ardavan-p/elec-491/gui/assets/gui_visual_v1.png

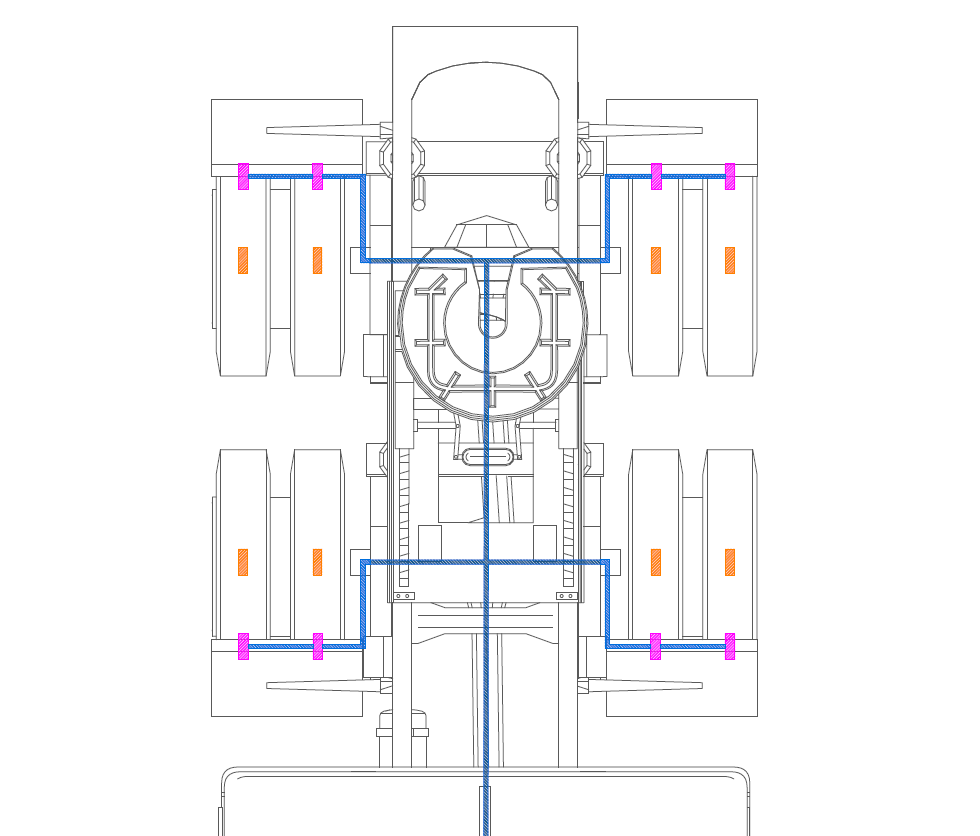
gui/assets/gui_visual_v1.png
