ardavan-p/elec-491/heat_map/tire.png

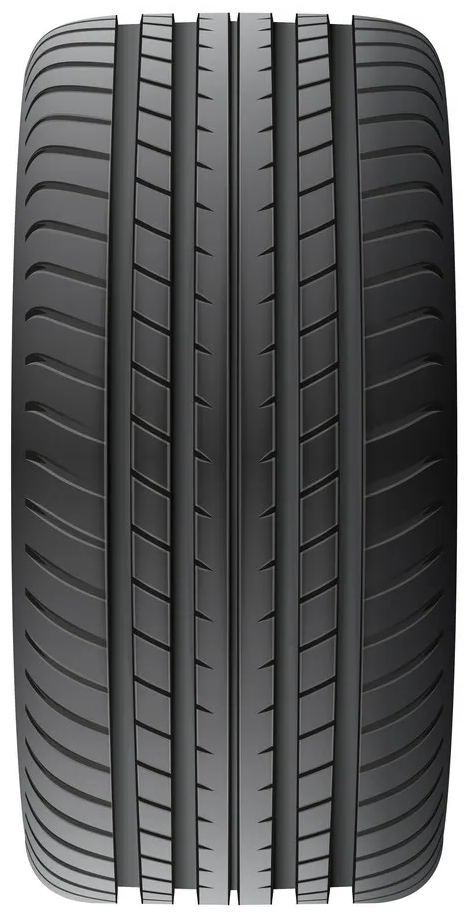
heat_map/tire.png
