ardavan-p/elec-491/heat_map/tire_cropped.png

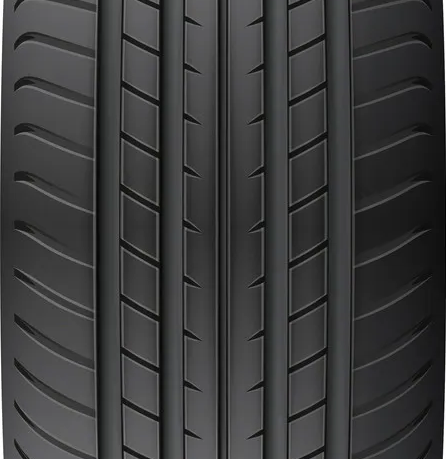
heat_map/tire_cropped.png
