ardavan-p/elec-491/heat_map/tire_rotated.png

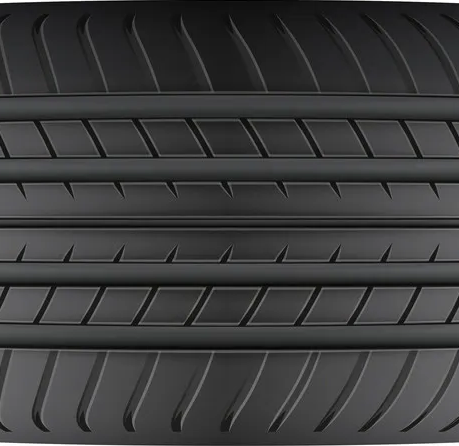
heat_map/tire_rotated.png
