ardavan-p/elec-491/heat_map/top-view-realistic-rubber-tire-symbol-vector-29433454.png

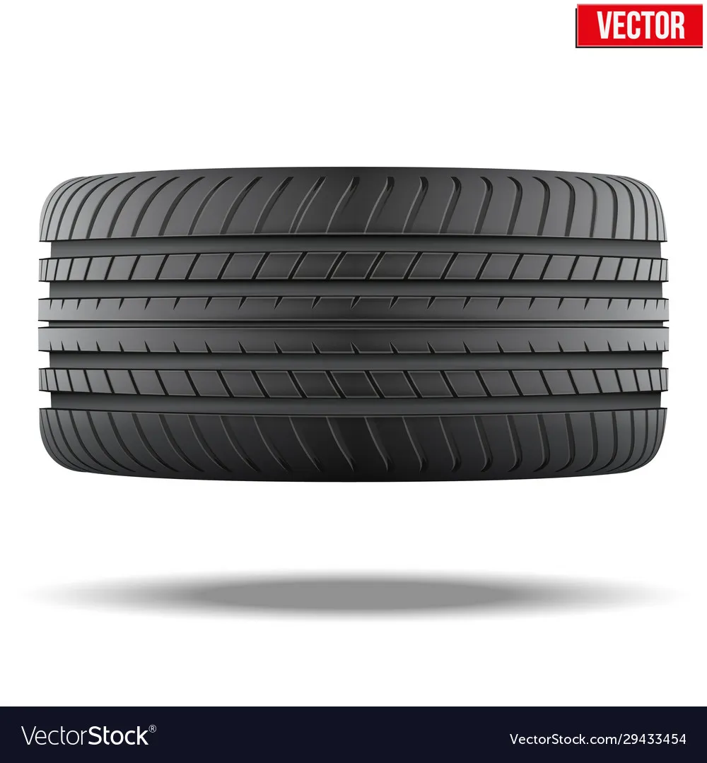
heat_map/top-view-realistic-rubber-tire-symbol-vector-29433454.png
