ardavan-p/elec-491/video/3d_animation/truck clip.PNG

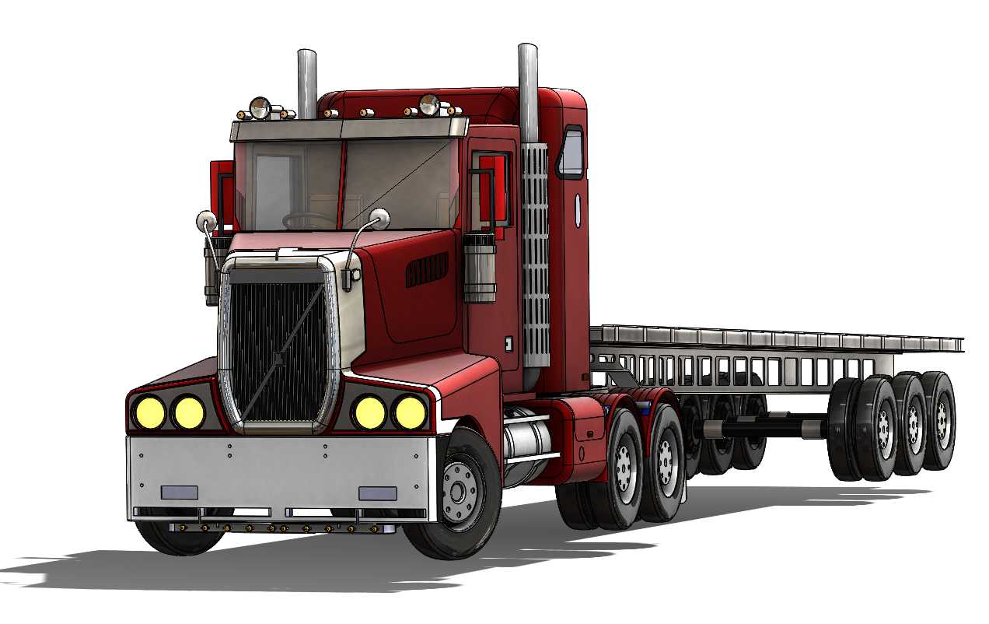
video/3d_animation/truck clip.PNG
