ardavan-p/elec-491/video/3d_animation/truck side view.PNG

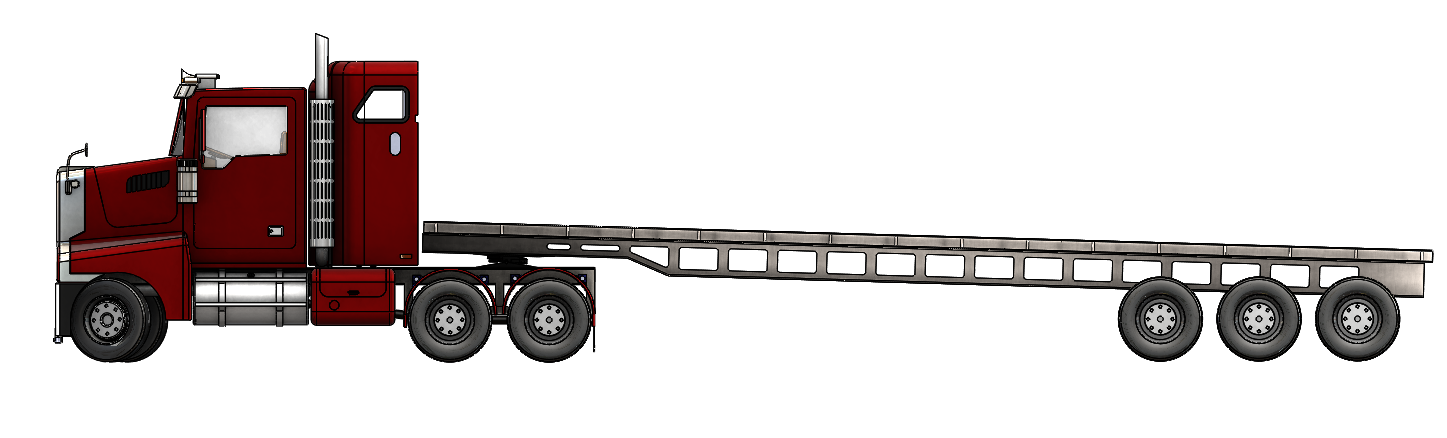
video/3d_animation/truck side view.PNG
