ardavan-p/elec-491/video/scene1/title_screen.png

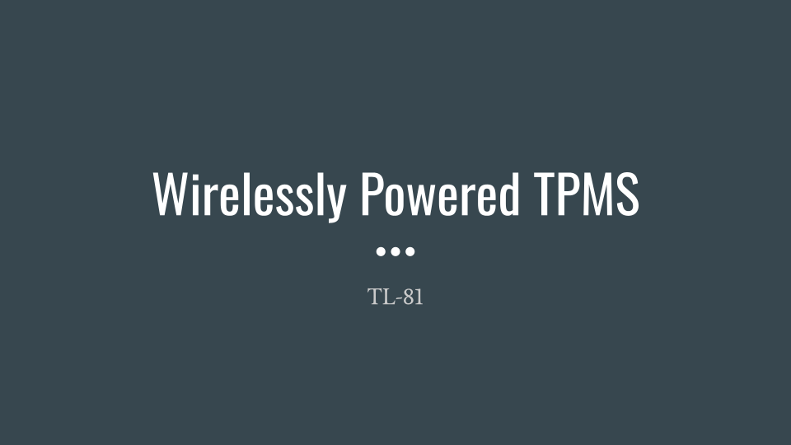
video/scene1/title_screen.png
