ardavan-p/elec-491/video/scene3/ptn_image_v2.png

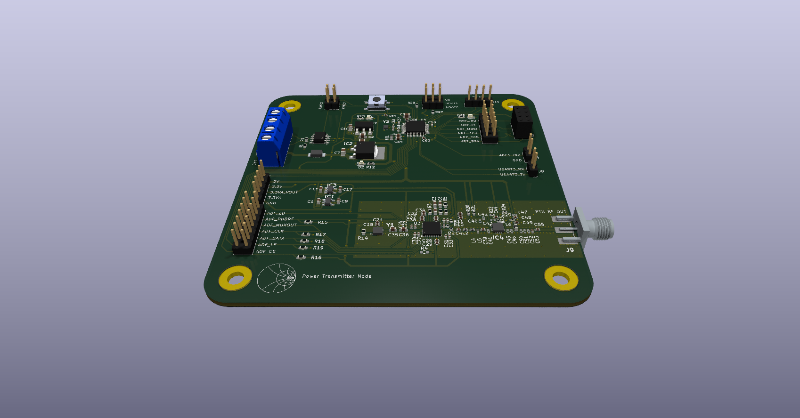
video/scene3/ptn_image_v2.png
