ardavan-p/elec-491/video/scene5/ECE.png

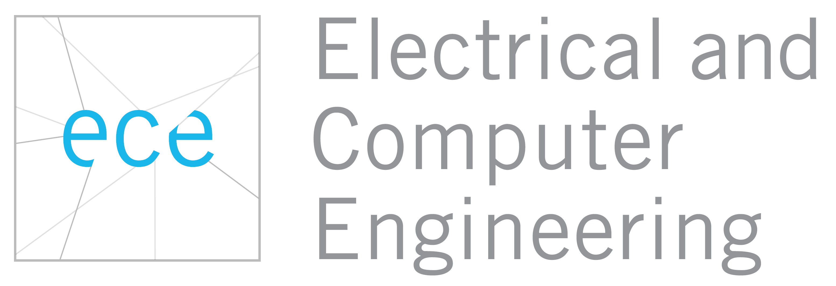
video/scene5/ECE.png
