ardavan-p/elec-491/enclosure/ptn/nRF_PCB.SLDPRT

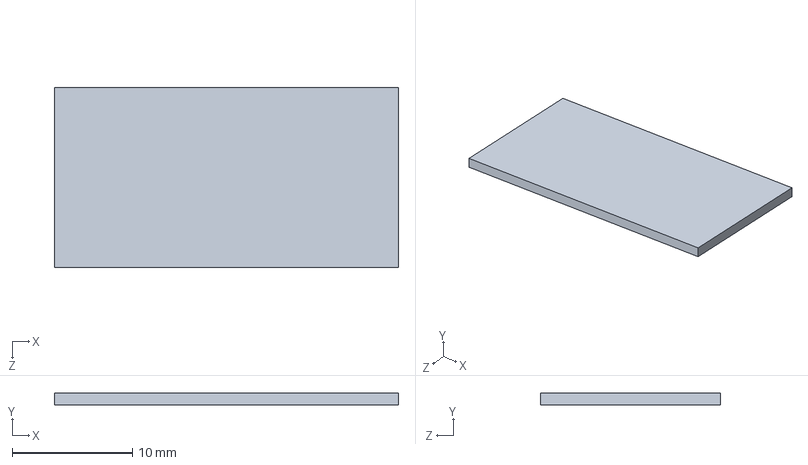
[picture p16: CAD file, 2024-08-16]
enclosure/ptn/nRF_PCB.SLDPRT
28.6 x 1.00 x 15.0 mm
