ardavan-p/elec-491/sn/footprints/capacitors/LIB_T520Y477M006ATE035/T520Y477M006ATE035/3D/T520Y477M006ATE035.stp

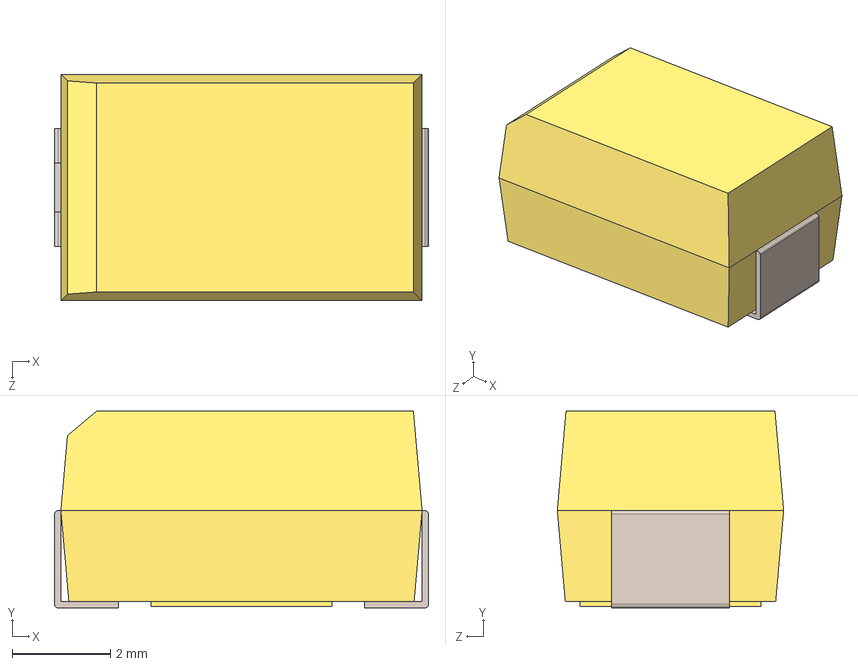
[picture p17: CAD file, 2024-07-30]
sn/footprints/capacitors/LIB_T520Y477M006ATE035/T520Y477M006ATE035/3D/T520Y477M006ATE035.stp
7.60 x 4.00 x 4.60 mm
Case_Bottom_31
Case_Top_31
Case_Cathode_31
Case_Anode_31
