ardavan-p/elec-491/sn/footprints/capacitors/LIB_TPMV108M006R0020/TPMV108M006R0020/3D/TPMV108M006R0020.stp

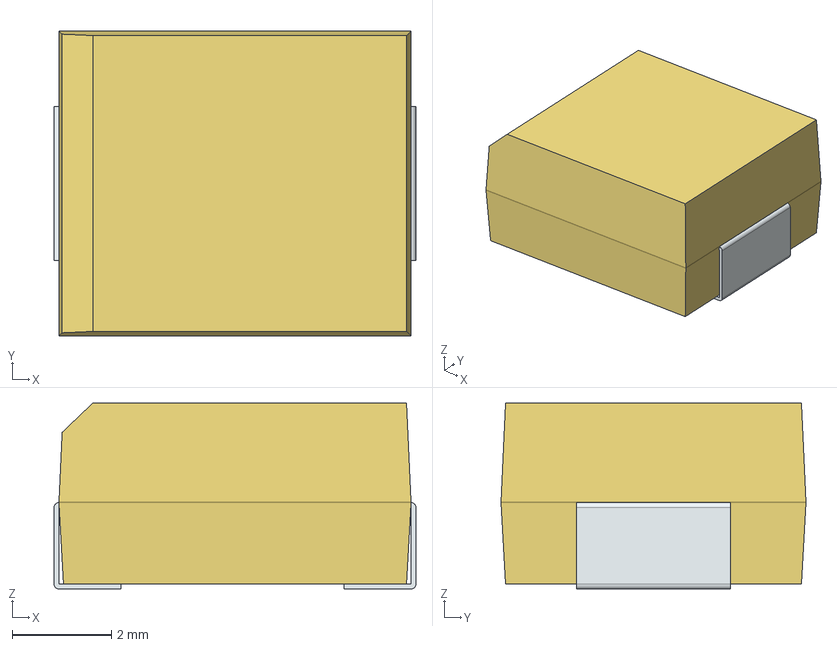
[picture p18: CAD file, 2024-07-30]
sn/footprints/capacitors/LIB_TPMV108M006R0020/TPMV108M006R0020/3D/TPMV108M006R0020.stp
7.30 x 6.15 x 3.75 mm
FilletPin1
FilletPin2
