ardavan-p/elec-491/sn/footprints/capacitors/LIB_TR3W108M6R3C0050/TR3W108M6R3C0050/3D/TR3W108M6R3C0050.stp

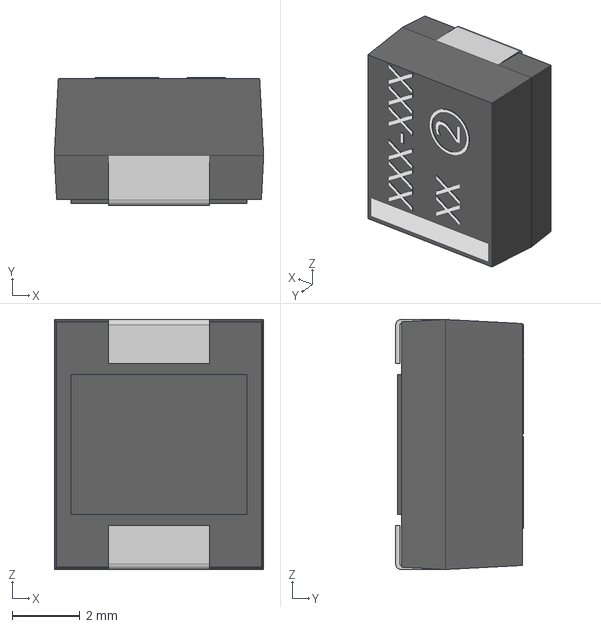
[picture p19: CAD file, 2024-07-30]
sn/footprints/capacitors/LIB_TR3W108M6R3C0050/TR3W108M6R3C0050/3D/TR3W108M6R3C0050.stp
6.20 x 3.78 x 7.40 mm
