ardavan-p/elec-491/sn/footprints/CONSMA020_062_G/CONSMA020.062-G.step

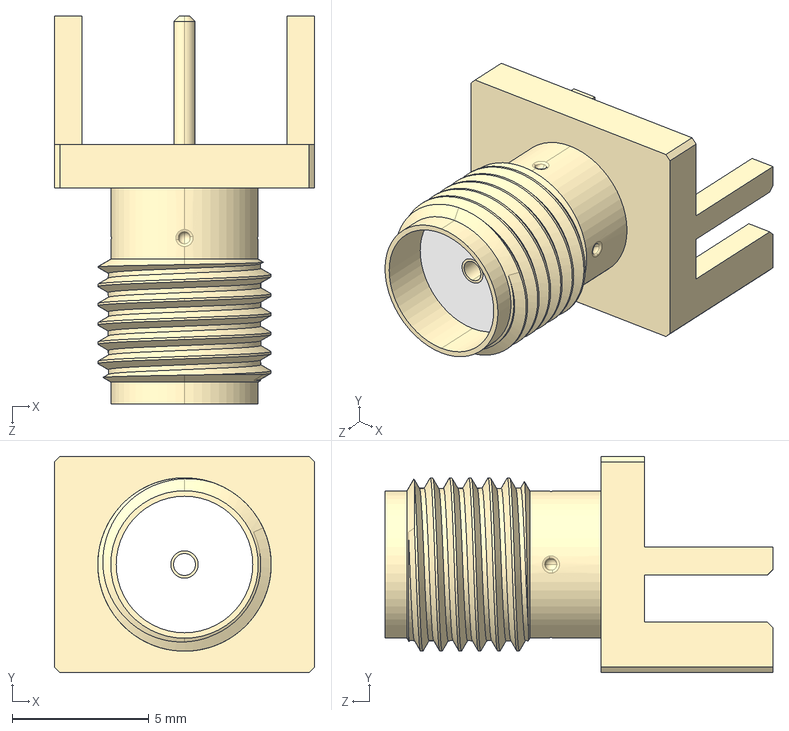
[picture p20: CAD file, 2024-07-30]
sn/footprints/CONSMA020_062_G/CONSMA020.062-G.step
9.52 x 7.92 x 14.2 mm
