ardavan-p/elec-491/sn/footprints/LIB_381LX473M016A452/381LX473M016A452/3D/381LX473M016A452.stp

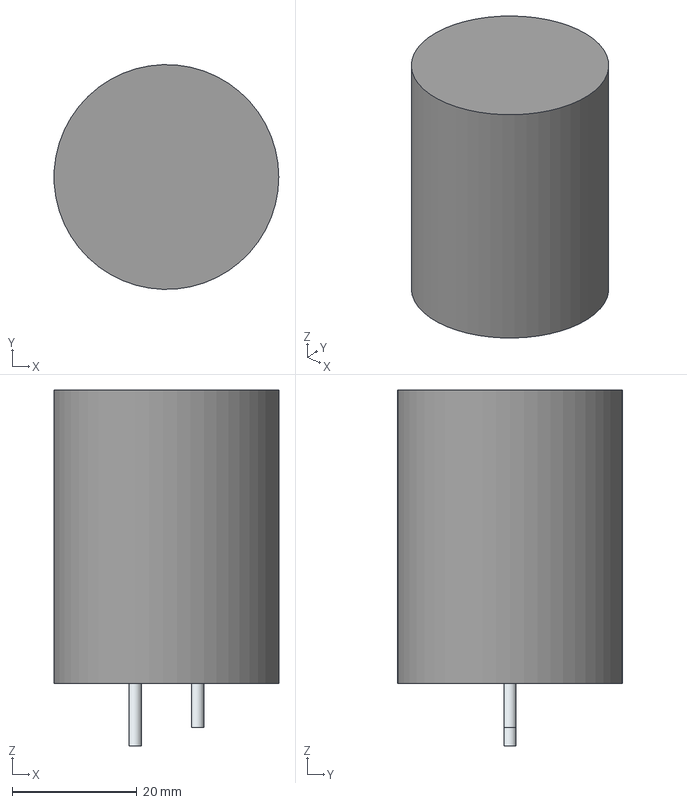
[picture p21: CAD file, 2024-07-30]
sn/footprints/LIB_381LX473M016A452/381LX473M016A452/3D/381LX473M016A452.stp
36.0 x 36.0 x 57.0 mm
SimpleBody
Pin1
Pin2
