ardavan-p/elec-491/sn/footprints/LIB_500SSP1S1M6QEB/500SSP1S1M6QEB/3D/500SSP1S1M6QEB.stp

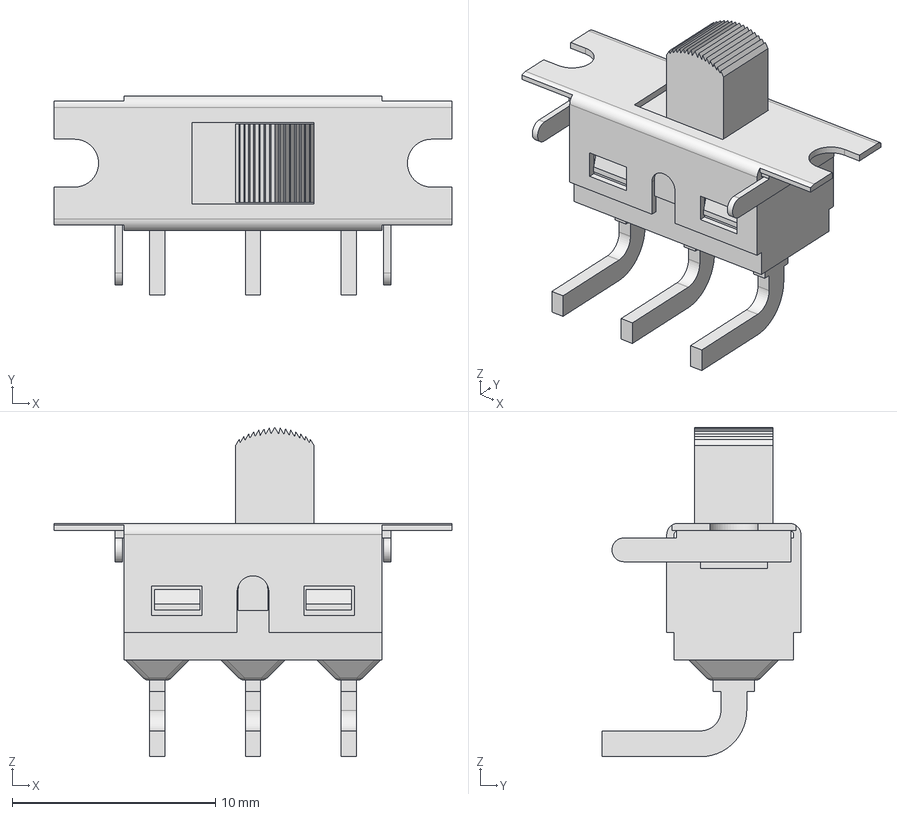
[picture p22: CAD file, 2024-07-30]
sn/footprints/LIB_500SSP1S1M6QEB/500SSP1S1M6QEB/3D/500SSP1S1M6QEB.stp
19.6 x 9.78 x 16.2 mm
