ardavan-p/elec-491/sn/footprints/LIB_901-10309/901-10309/3D/901-10309.stp

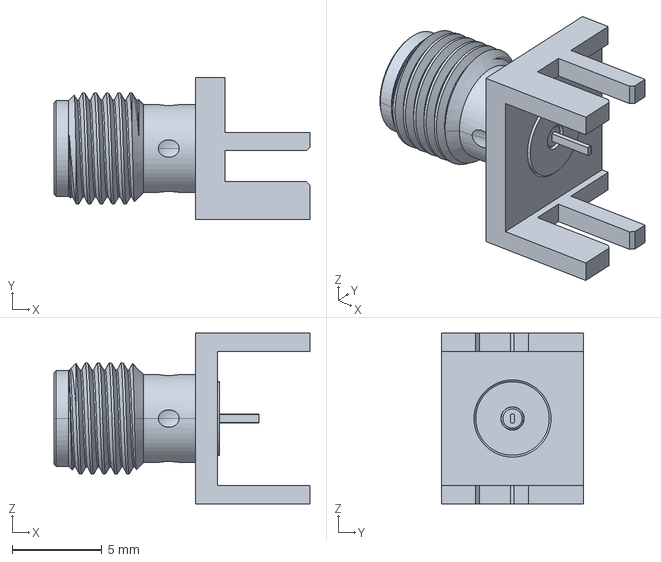
[picture p23: CAD file, 2024-07-30]
sn/footprints/LIB_901-10309/901-10309/3D/901-10309.stp
14.3 x 7.92 x 9.52 mm
