ardavan-p/elec-491/sn/footprints/LIB_AD8226ARMZ/AD8226ARMZ/3D/AD8226ARMZ.stp

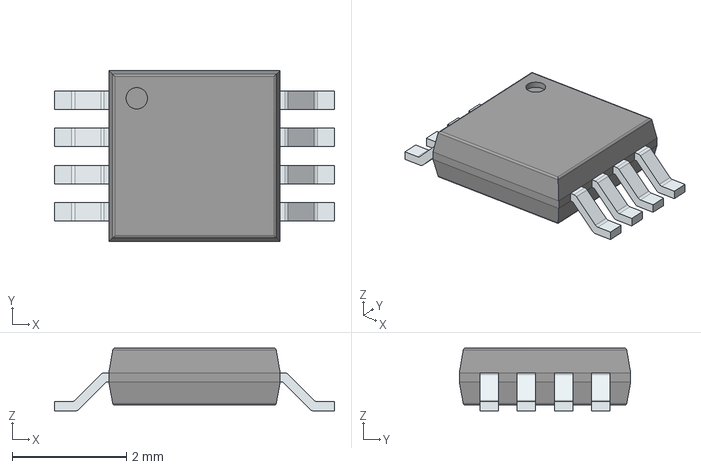
[picture p24: CAD file, 2024-07-30]
sn/footprints/LIB_AD8226ARMZ/AD8226ARMZ/3D/AD8226ARMZ.stp
4.90 x 3.00 x 1.10 mm
PinsArrayLR
