ardavan-p/elec-491/sn/footprints/LIB_AYZ0102AGRLC/AYZ0102AGRLC/3D/AYZ0102AGRLC.stp

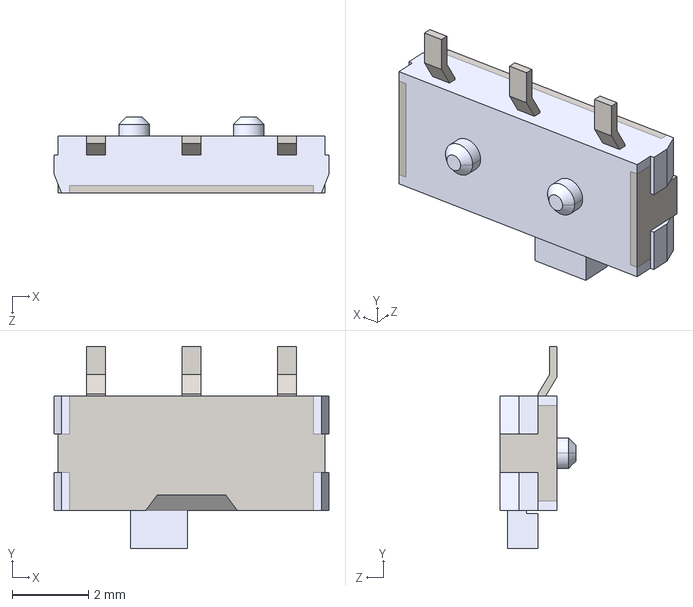
[picture p25: CAD file, 2024-07-30]
sn/footprints/LIB_AYZ0102AGRLC/AYZ0102AGRLC/3D/AYZ0102AGRLC.stp
7.20 x 5.30 x 2.00 mm
