ardavan-p/elec-491/sn/footprints/LIB_B3FS-1002P/B3FS-1002P/3D/B3FS-1002P.stp

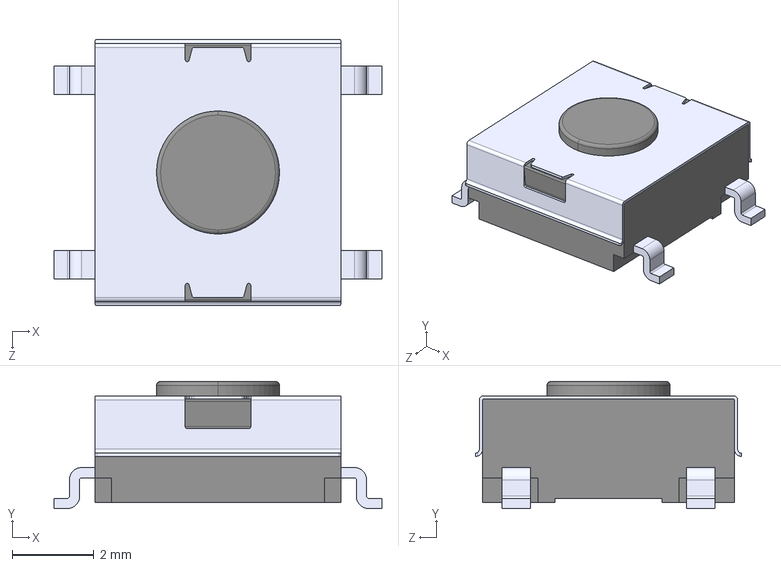
[picture p26: CAD file, 2024-07-30]
sn/footprints/LIB_B3FS-1002P/B3FS-1002P/3D/B3FS-1002P.stp
8.00 x 3.10 x 6.50 mm
