ardavan-p/elec-491/sn/footprints/LIB_CAS-120A1/CAS-120A1/3D/CAS-120A1.stp

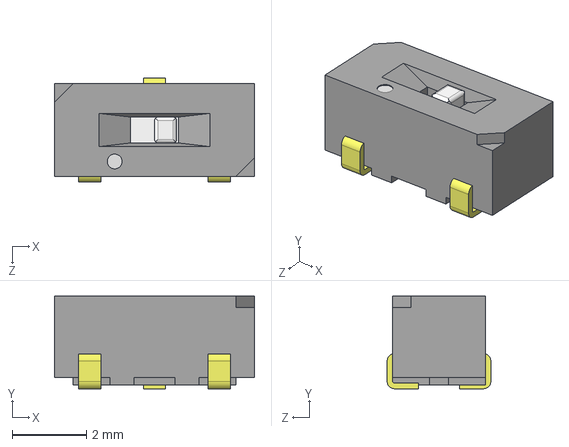
[picture p27: CAD file, 2024-07-30]
sn/footprints/LIB_CAS-120A1/CAS-120A1/3D/CAS-120A1.stp
5.40 x 2.50 x 2.80 mm
1 pole_s
CAS_c_12A
