ardavan-p/elec-491/sn/footprints/LIB_EEE-FP0J102AL/EEE-FP0J102AL/3D/EEE-FP0J102AL.stp

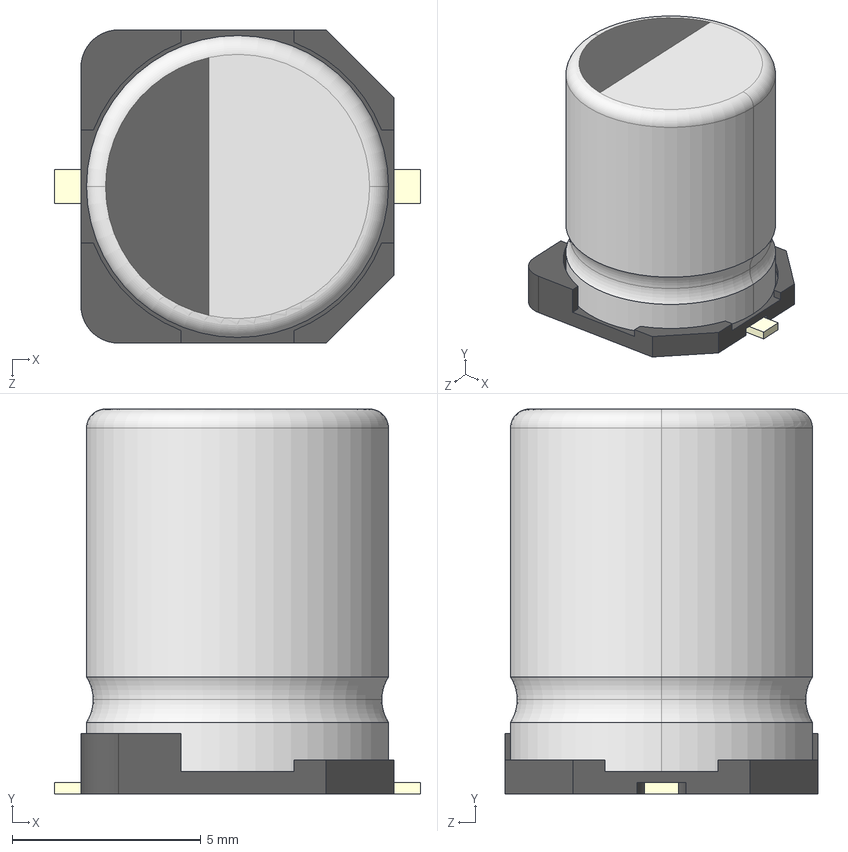
[picture p28: CAD file, 2024-07-30]
sn/footprints/LIB_EEE-FP0J102AL/EEE-FP0J102AL/3D/EEE-FP0J102AL.stp
9.70 x 10.2 x 8.30 mm
標準SIZE CODE F-001
標準SIZE CODE F-002
標準SIZE CODE F-003 x 2
