ardavan-p/elec-491/sn/footprints/LIB_EMPCB.SMAFSTJ.B.HT/EMPCB.SMAFSTJ.B.HT/3D/EMPCB.SMAFSTJ.B.HT.stp

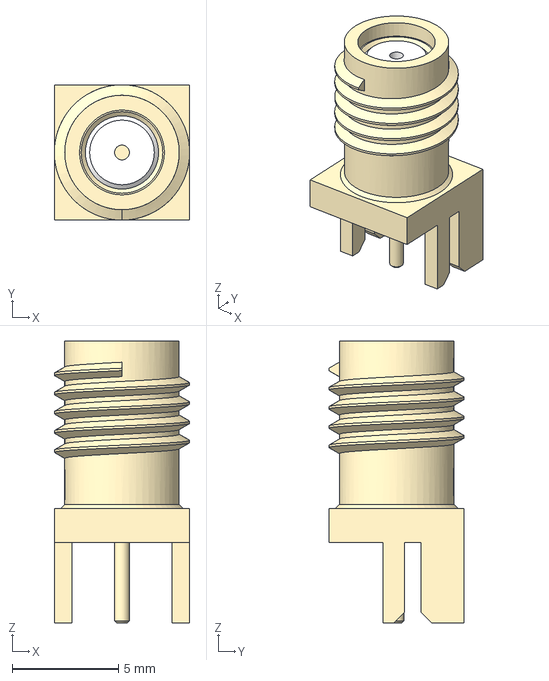
[picture p29: CAD file, 2024-07-30]
sn/footprints/LIB_EMPCB.SMAFSTJ.B.HT/EMPCB.SMAFSTJ.B.HT/3D/EMPCB.SMAFSTJ.B.HT.stp
6.38 x 6.39 x 13.3 mm
