ardavan-p/elec-491/sn/footprints/LIB_FME0H473ZF/FME0H473ZF/3D/FME0H473ZF.stp

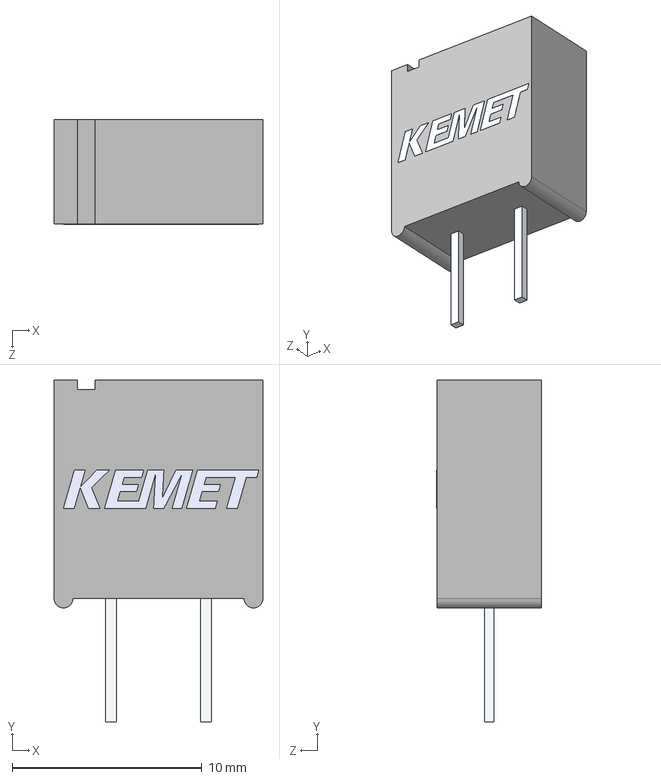
[picture p30: CAD file, 2024-07-30]
sn/footprints/LIB_FME0H473ZF/FME0H473ZF/3D/FME0H473ZF.stp
11.0 x 18.0 x 5.50 mm
