ardavan-p/elec-491/sn/footprints/LIB_NPP-301A-700AT/NPP-301A-700AT/3D/NPP-301A-700AT.stp

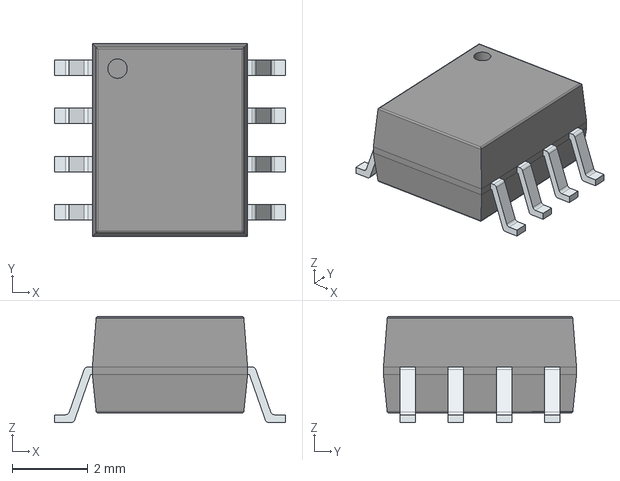
[picture p31: CAD file, 2024-07-30]
sn/footprints/LIB_NPP-301A-700AT/NPP-301A-700AT/3D/NPP-301A-700AT.stp
6.10 x 5.10 x 2.80 mm
PinsArrayLR
