ardavan-p/elec-491/sn/footprints/LIB_nRF24L01P/nRF24L01P/3D/nRF24L01P.stp

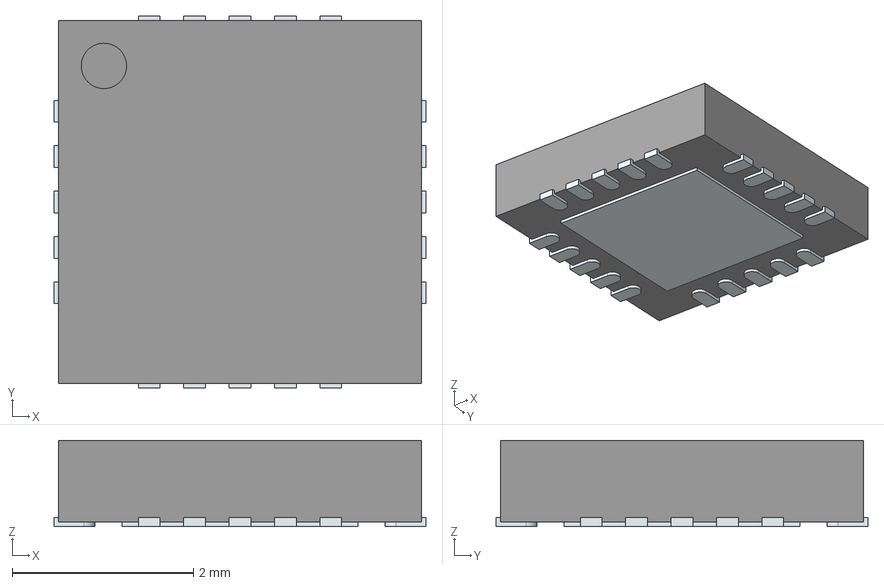
[picture p32: CAD file, 2024-07-30]
sn/footprints/LIB_nRF24L01P/nRF24L01P/3D/nRF24L01P.stp
4.10 x 4.10 x 0.95 mm
ThermalPin
PinsArrayLR
PinsArrayTB
