ardavan-p/elec-491/sn/footprints/LIB_P2110B/P2110B/3D/P2110B.stp

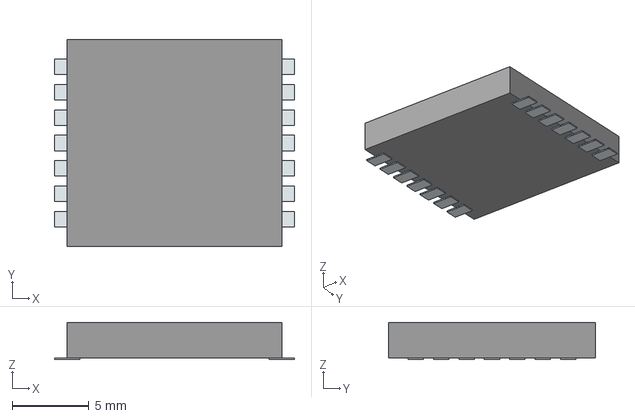
[picture p33: CAD file, 2024-07-30]
sn/footprints/LIB_P2110B/P2110B/3D/P2110B.stp
15.6 x 13.5 x 2.41 mm
Pins
