ardavan-p/elec-491/sn/footprints/LIB_STM32U031K8U6/STM32U031K8U6/3D/STM32U031K8U6.stp

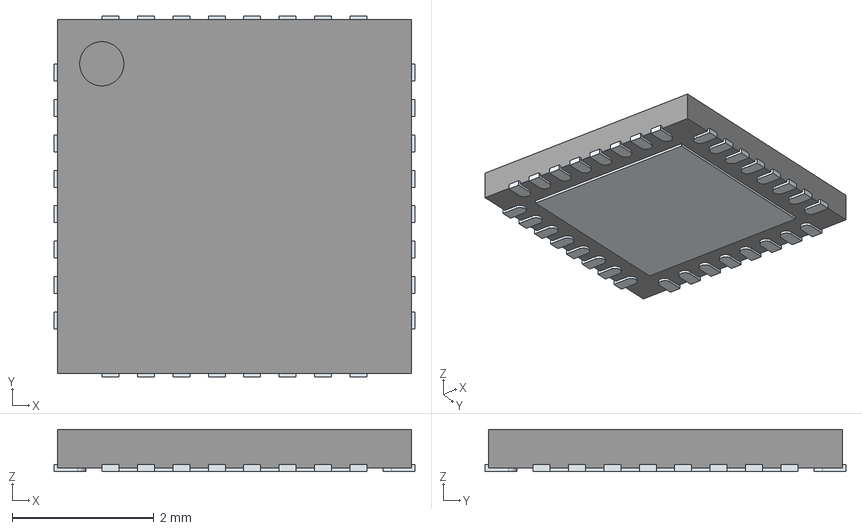
[picture p34: CAD file, 2024-07-30]
sn/footprints/LIB_STM32U031K8U6/STM32U031K8U6/3D/STM32U031K8U6.stp
5.10 x 5.10 x 0.6 mm
ThermalPin
PinsArrayLR
PinsArrayTB
