ardavan-p/elec-491/sn/footprints/LIB_TS21-34-035-BK-160-SMT-TR/TS21-34-035-BK-160-SMT-TR/3D/TS21-34-035-BK-160-SMT-TR.stp

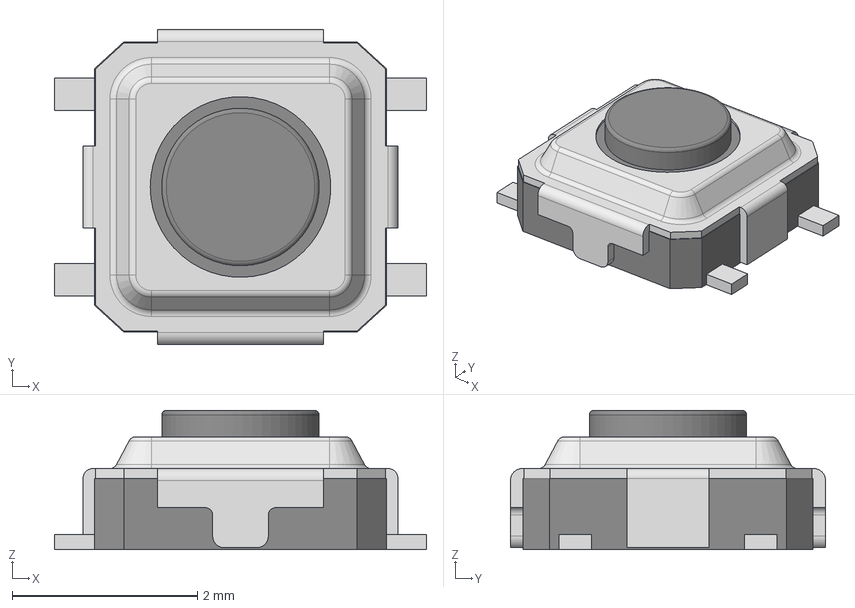
[picture p35: CAD file, 2024-07-30]
sn/footprints/LIB_TS21-34-035-BK-160-SMT-TR/TS21-34-035-BK-160-SMT-TR/3D/TS21-34-035-BK-160-SMT-TR.stp
4.02 x 3.40 x 1.50 mm
