ardavan-p/elec-491/sn/footprints/ul_STM32U031R8T6/LQFP64_STM.step

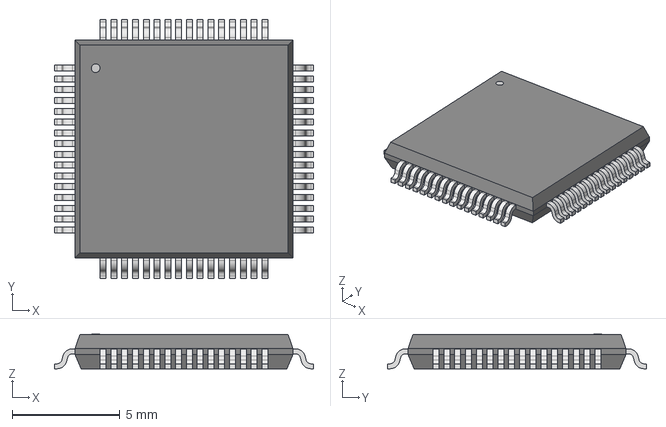
[picture p36: CAD file, 2024-07-30]
sn/footprints/ul_STM32U031R8T6/LQFP64_STM.step
12.0 x 12.0 x 1.60 mm
