ardavan-p/elec-491/video/3d_animation/BGs flatbed 2/mud guard back.SLDPRT

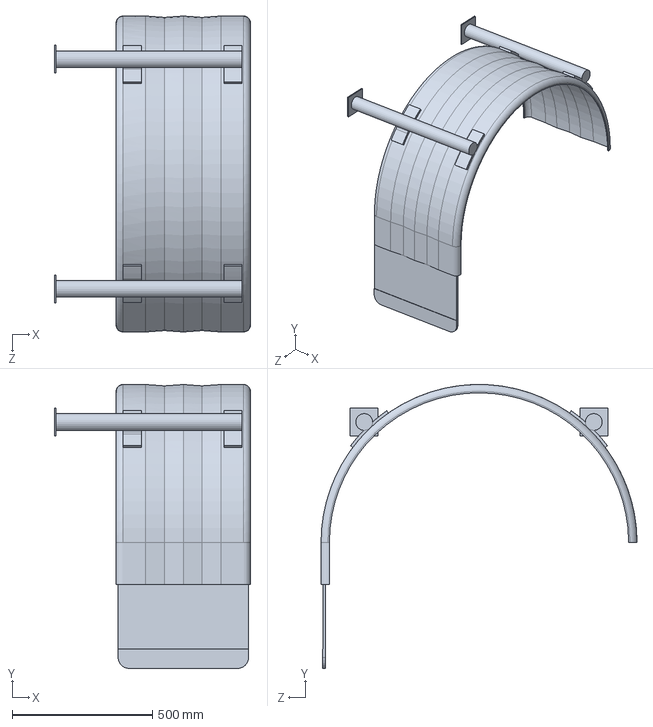
[picture p37: CAD file, 2024-08-16]
video/3d_animation/BGs flatbed 2/mud guard back.SLDPRT
700.0 x 1013.8 x 1128.0 mm
