ardavan-p/elec-491/enclosure/ptn/baseplate.SLDPRT

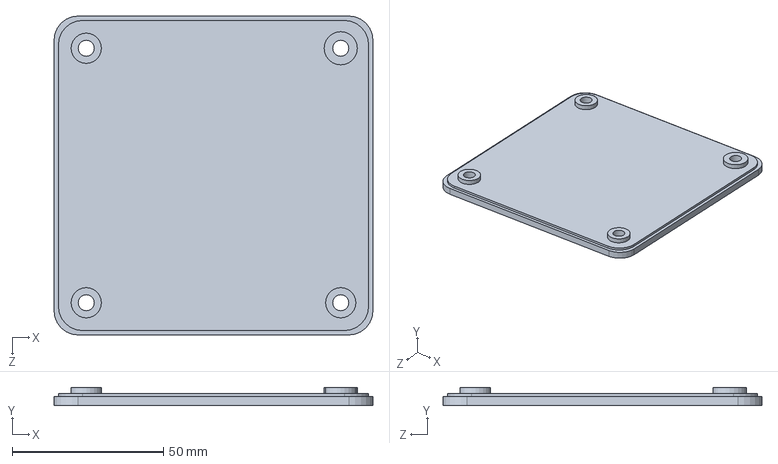
[picture p38: CAD file, 2024-08-16]
enclosure/ptn/baseplate.SLDPRT
105.3 x 6.00 x 105.3 mm
