ardavan-p/elec-491/video/3d_animation/BGs flatbed 2/attachment lock.SLDPRT

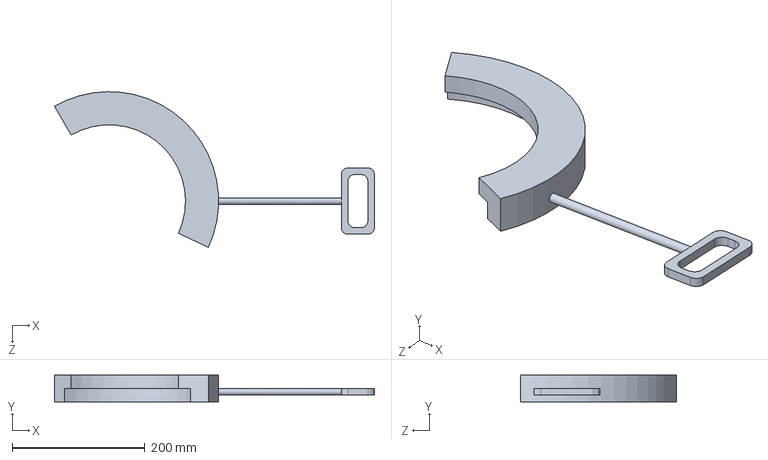
[picture p39: CAD file, 2024-08-16]
video/3d_animation/BGs flatbed 2/attachment lock.SLDPRT
482.5 x 40.0 x 234.7 mm
