ardavan-p/elec-491/enclosure/ptn/top_cover.SLDPRT

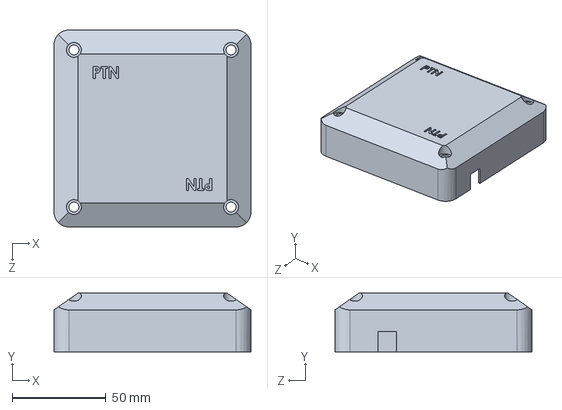
[picture p40: CAD file, 2024-08-16]
enclosure/ptn/top_cover.SLDPRT
105.3 x 31.5 x 105.3 mm
