ardavan-p/elec-491/video/3d_animation/BGs flatbed 2/right door.SLDPRT

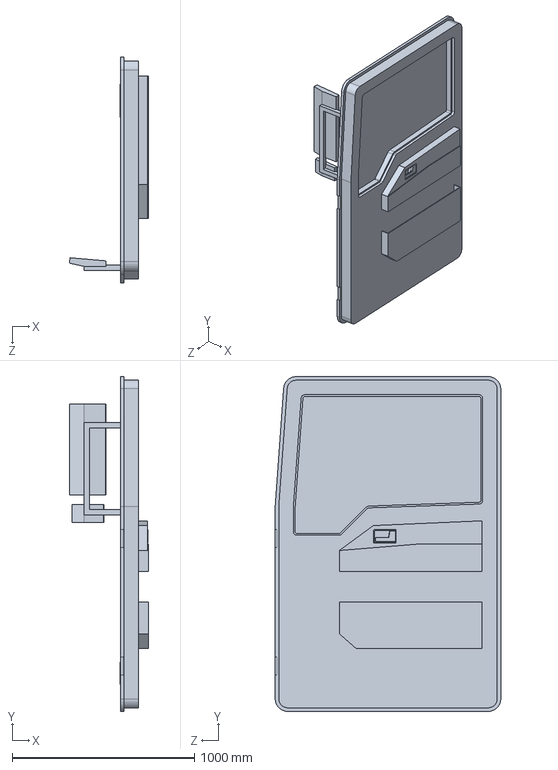
[picture p41: CAD file, 2024-08-16]
video/3d_animation/BGs flatbed 2/right door.SLDPRT
434.2 x 1840.0 x 1240.0 mm
