ardavan-p/elec-491/video/3d_animation/BGs flatbed 2/steering.sldprt

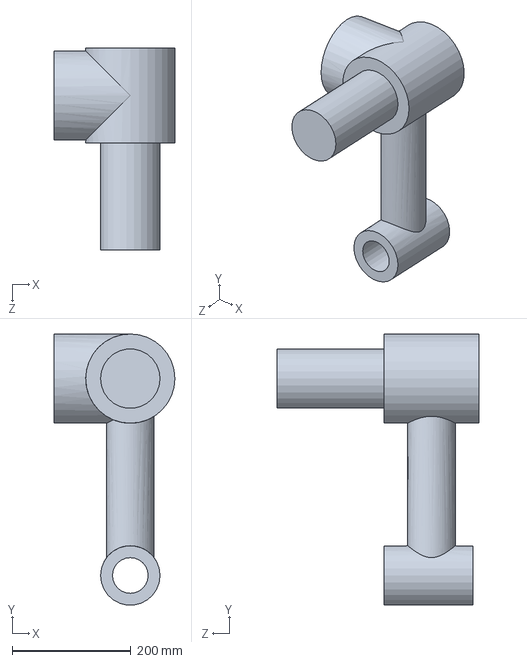
[picture p42: CAD file, 2024-08-16]
video/3d_animation/BGs flatbed 2/steering.sldprt
203.2 x 455.6 x 340.0 mm
