ardavan-p/elec-491/video/3d_animation/BGs flatbed 2/hub.SLDPRT

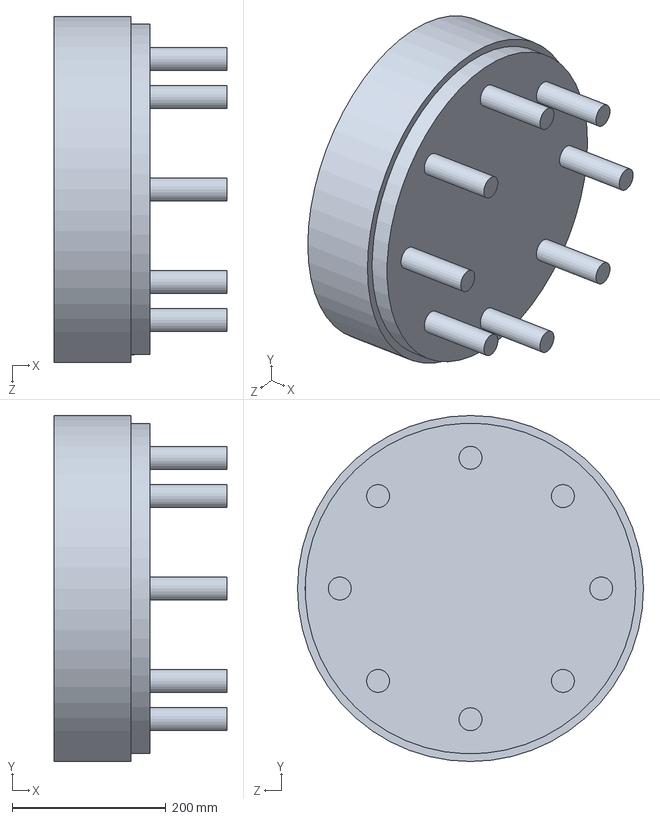
[picture p43: CAD file, 2024-08-16]
video/3d_animation/BGs flatbed 2/hub.SLDPRT
225.0 x 450.0 x 450.0 mm
