ardavan-p/elec-491/video/3d_animation/BGs flatbed 2/tank.SLDPRT

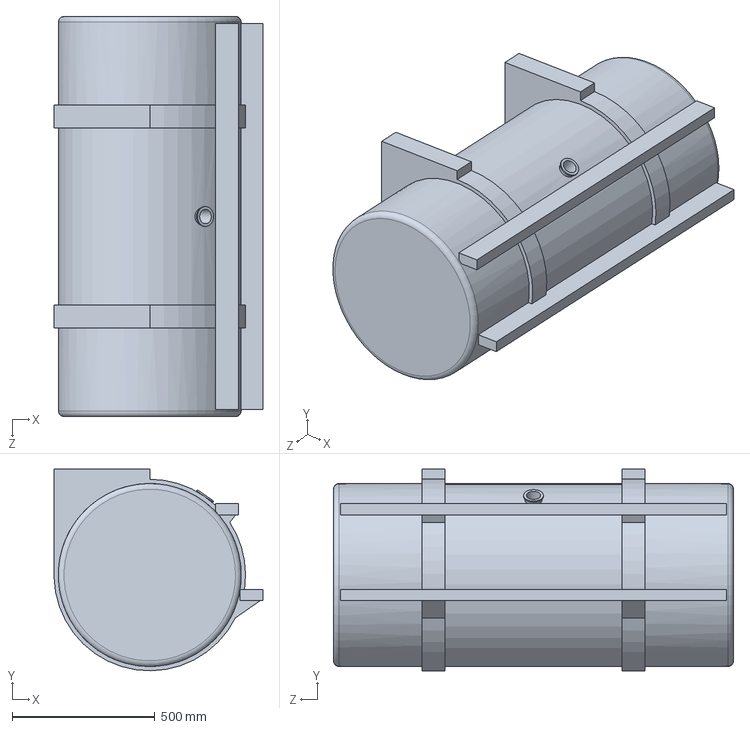
[picture p44: CAD file, 2024-08-16]
video/3d_animation/BGs flatbed 2/tank.SLDPRT
731.1 x 705.0 x 1400.0 mm
