ardavan-p/elec-491/video/3d_animation/BGs flatbed 2/mud guard2 front.SLDPRT

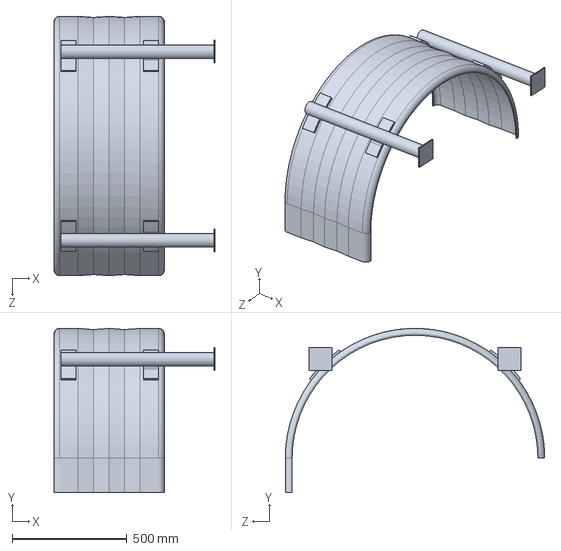
[picture p45: CAD file, 2024-08-16]
video/3d_animation/BGs flatbed 2/mud guard2 front.SLDPRT
700.0 x 713.8 x 1128.0 mm
