ardavan-p/elec-491/video/3d_animation/BGs flatbed 2/cab.SLDPRT

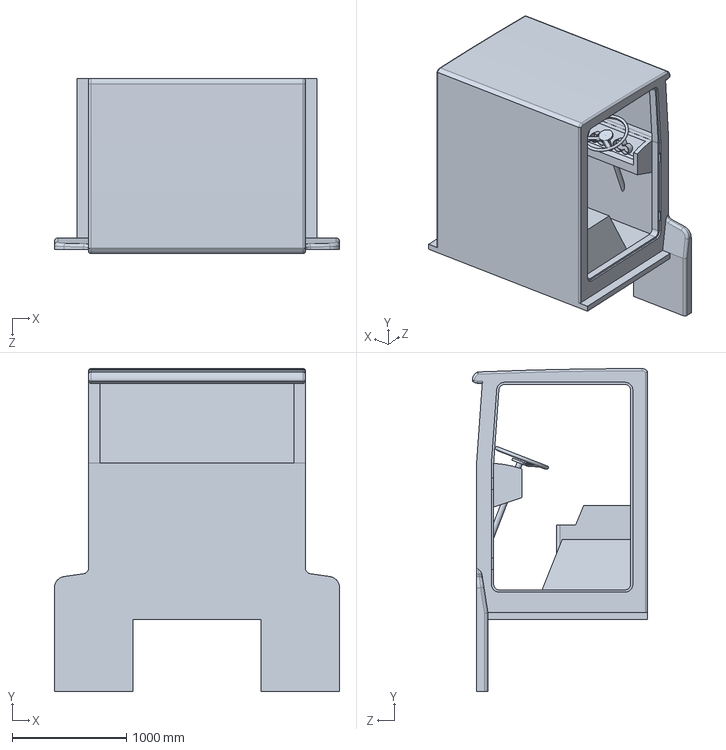
[picture p46: CAD file, 2024-08-16]
video/3d_animation/BGs flatbed 2/cab.SLDPRT
2500.0 x 2830.0 x 1537.6 mm
