ardavan-p/elec-491/video/3d_animation/BGs flatbed 2/bonnet.SLDPRT

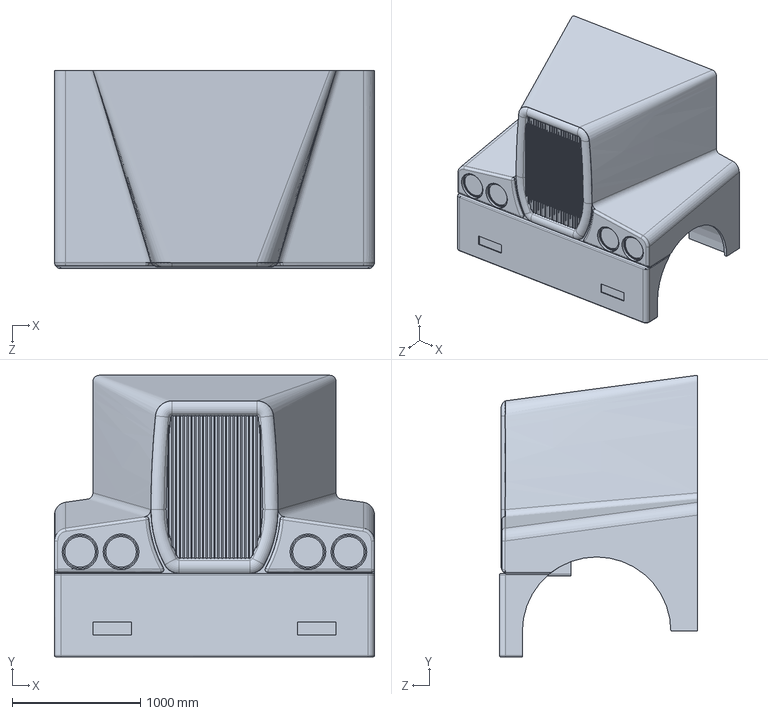
[picture p47: CAD file, 2024-08-16]
video/3d_animation/BGs flatbed 2/bonnet.SLDPRT
2500.0 x 2200.0 x 1550.0 mm
