ardavan-p/elec-491/video/3d_animation/BGs flatbed 2/drive shaft connector.SLDPRT

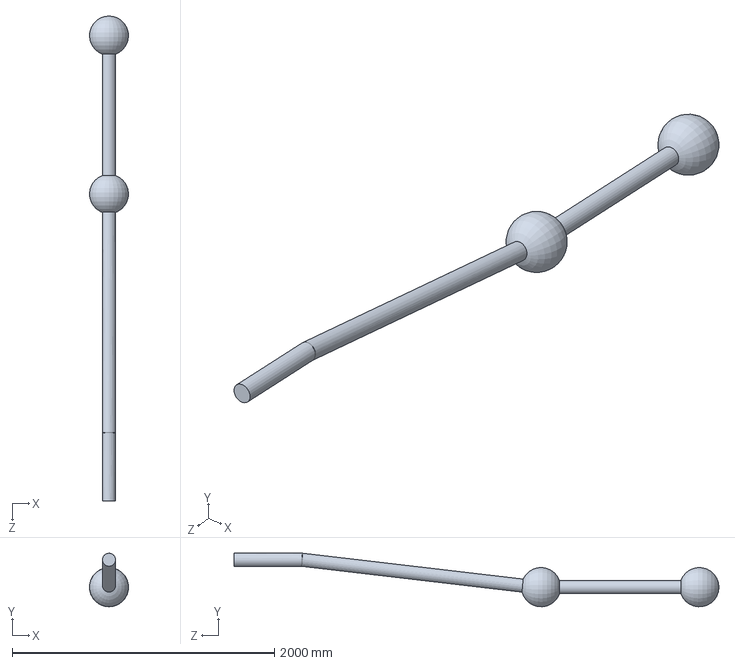
[picture p48: CAD file, 2024-08-16]
video/3d_animation/BGs flatbed 2/drive shaft connector.SLDPRT
297.2 x 409.0 x 3700.7 mm
