ardavan-p/elec-491/video/3d_animation/BGs flatbed 2/Copy of steering.sldprt

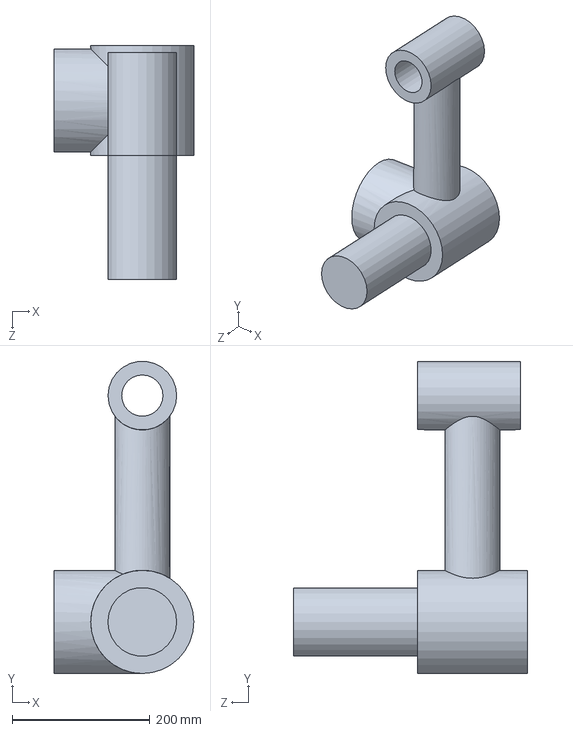
[picture p49: CAD file, 2024-08-16]
video/3d_animation/BGs flatbed 2/Copy of steering.sldprt
203.2 x 453.6 x 340.0 mm
