ardavan-p/elec-491/video/3d_animation/BGs flatbed 2/rear tyre.SLDPRT

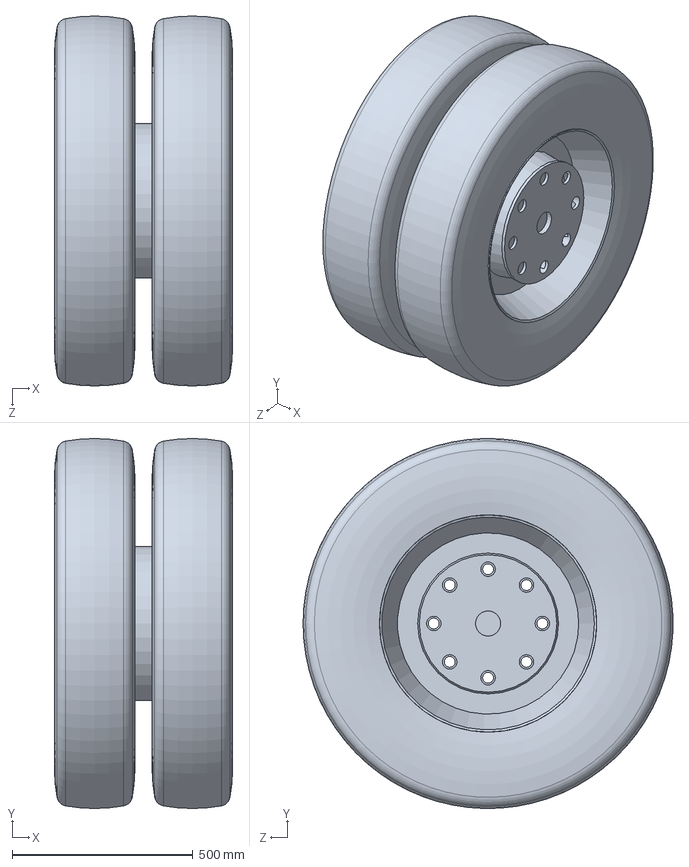
[picture p50: CAD file, 2024-08-16]
video/3d_animation/BGs flatbed 2/rear tyre.SLDPRT
492.4 x 1022.3 x 1022.0 mm
