ardavan-p/elec-491/video/3d_animation/BGs flatbed 2/seat.SLDPRT

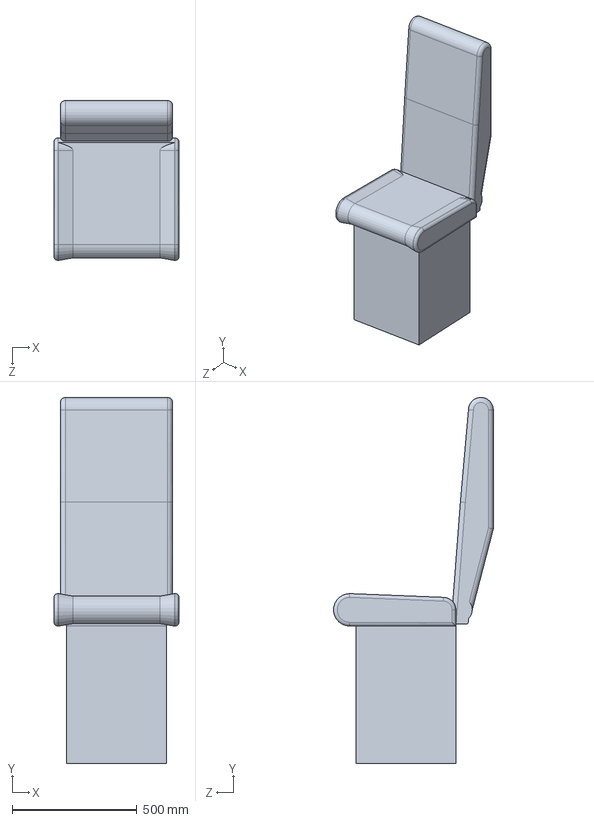
[picture p51: CAD file, 2024-08-16]
video/3d_animation/BGs flatbed 2/seat.SLDPRT
500.0 x 1464.7 x 639.6 mm
