ardavan-p/elec-491/video/3d_animation/BGs flatbed 2/CAT 3126 SIMPLIFIED.SLDPRT

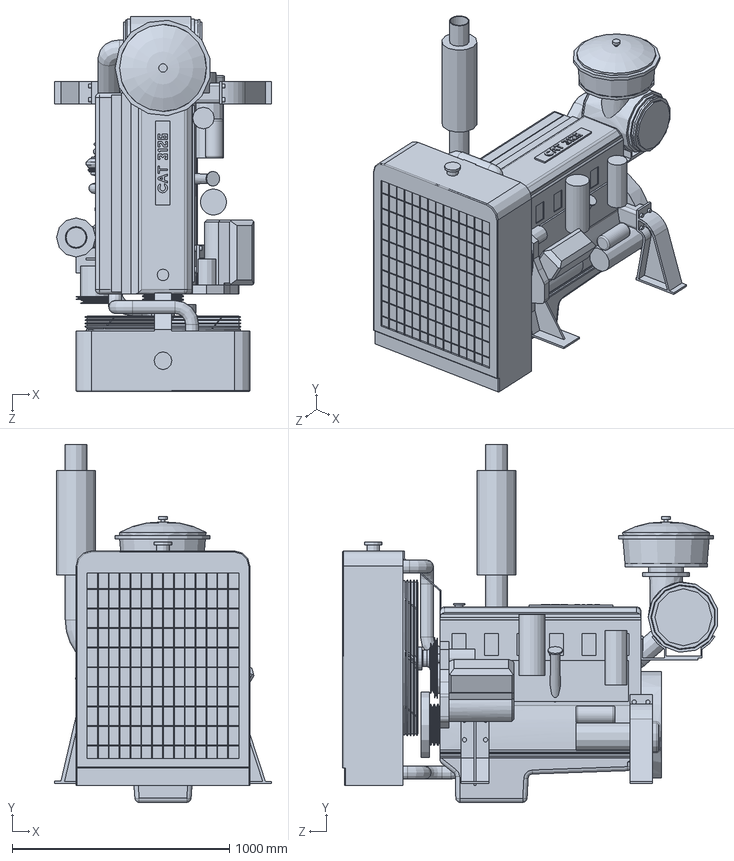
[picture p52: CAD file, 2024-08-16]
video/3d_animation/BGs flatbed 2/CAT 3126 SIMPLIFIED.SLDPRT
1000.0 x 1647.9 x 1727.6 mm
