ardavan-p/elec-491/video/3d_animation/BGs flatbed 2/tr. bk axles.SLDPRT

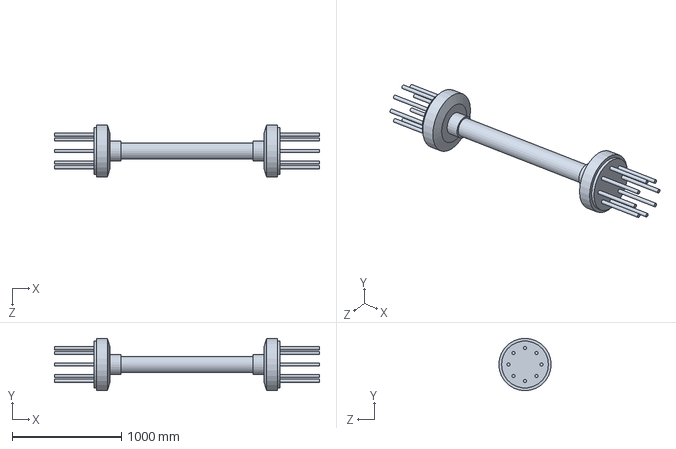
[picture p53: CAD file, 2024-08-16]
video/3d_animation/BGs flatbed 2/tr. bk axles.SLDPRT
2430.0 x 480.0 x 480.0 mm
