ardavan-p/elec-491/video/3d_animation/sensor_node_model/SN_Assembly.SLDASM

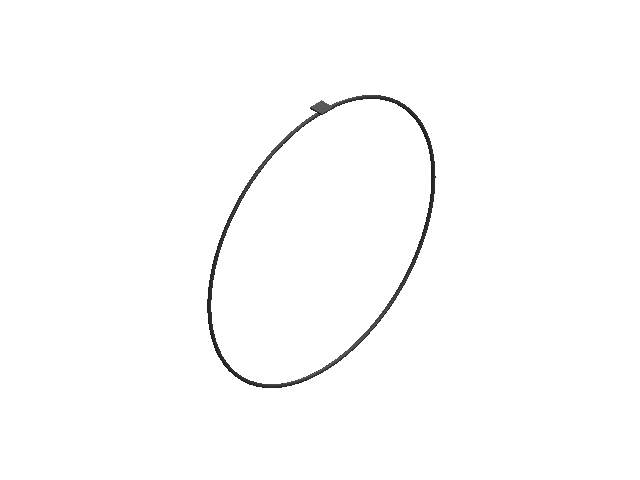
[picture p54: CAD file, 2024-08-16]
video/3d_animation/sensor_node_model/SN_Assembly.SLDASM
SN_enclosure_pouch
SN_enclosure_cover
SN_antenna_array_ring
R_0402_1005Metric-0_1 x 12
C_0402_1005Metric-1_1 x 16
SOT_353_SC_70_5_1
QFN-20-1EP_4x4mm_Pitch0.5mm_1
LED_0402_1005Metric-2_1 x 2
L_0402_1005Metric-3_1 x 3
sensor-node-rev-2_track_1
sensor-node-rev-2_track_2
sensor-node-rev-2_track_3
sensor-node-rev-2_track_4
sensor-node-rev-2_track_5
sensor-node-rev-2_track_6
sensor-node-rev-2_track_7
sensor-node-rev-2_track_8
sensor-node-rev-2_track_9
sensor-node-rev-2_track_10
sensor-node-rev-2_track_11
sensor-node-rev-2_track_12
sensor-node-rev-2_track_13
sensor-node-rev-2_track_14
sensor-node-rev-2_track_15
sensor-node-rev-2_track_16
sensor-node-rev-2_track_17
sensor-node-rev-2_track_18
sensor-node-rev-2_track_19
sensor-node-rev-2_track_20
sensor-node-rev-2_track_21
sensor-node-rev-2_track_22
sensor-node-rev-2_track_23
sensor-node-rev-2_track_24
sensor-node-rev-2_track_25
sensor-node-rev-2_track_26
sensor-node-rev-2_track_27
sensor-node-rev-2_track_28
sensor-node-rev-2_track_29
sensor-node-rev-2_track_30
sensor-node-rev-2_track_31
sensor-node-rev-2_track_32
sensor-node-rev-2_track_33
sensor-node-rev-2_track_34
sensor-node-rev-2_track_35
sensor-node-rev-2_track_36
sensor-node-rev-2_track_37
sensor-node-rev-2_track_38
sensor-node-rev-2_track_39
sensor-node-rev-2_track_40
sensor-node-rev-2_track_41
sensor-node-rev-2_track_42
sensor-node-rev-2_track_43
sensor-node-rev-2_track_44
sensor-node-rev-2_track_45
sensor-node-rev-2_track_46
sensor-node-rev-2_track_47
sensor-node-rev-2_track_48
sensor-node-rev-2_track_49
sensor-node-rev-2_track_50
sensor-node-rev-2_track_51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
