ardavan-p/elec-491/enclosure/ptn/exports/Assembly2.gif

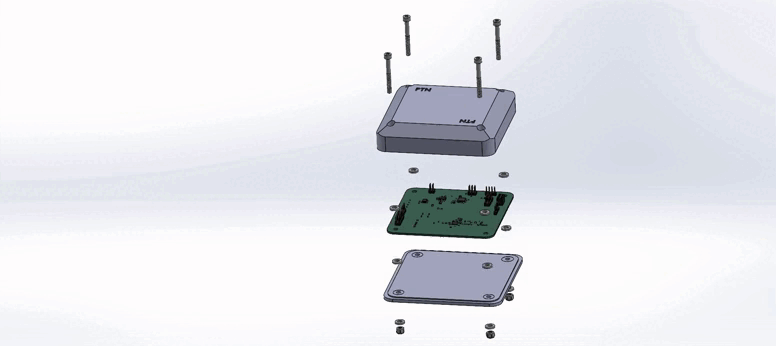
enclosure/ptn/exports/Assembly2.gif
