ardavan-p/elec-491/video/scene4/radio_waves-ezgif.com-gif-maker.gif

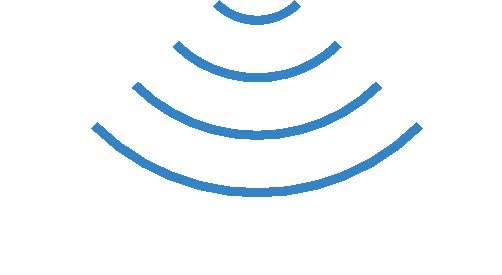
video/scene4/radio_waves-ezgif.com-gif-maker.gif
