ardavan-p/elec-491/sn/rev-2/pcb/sensor-node-rev-2/sensor-node-rev-2-schematic.pdf

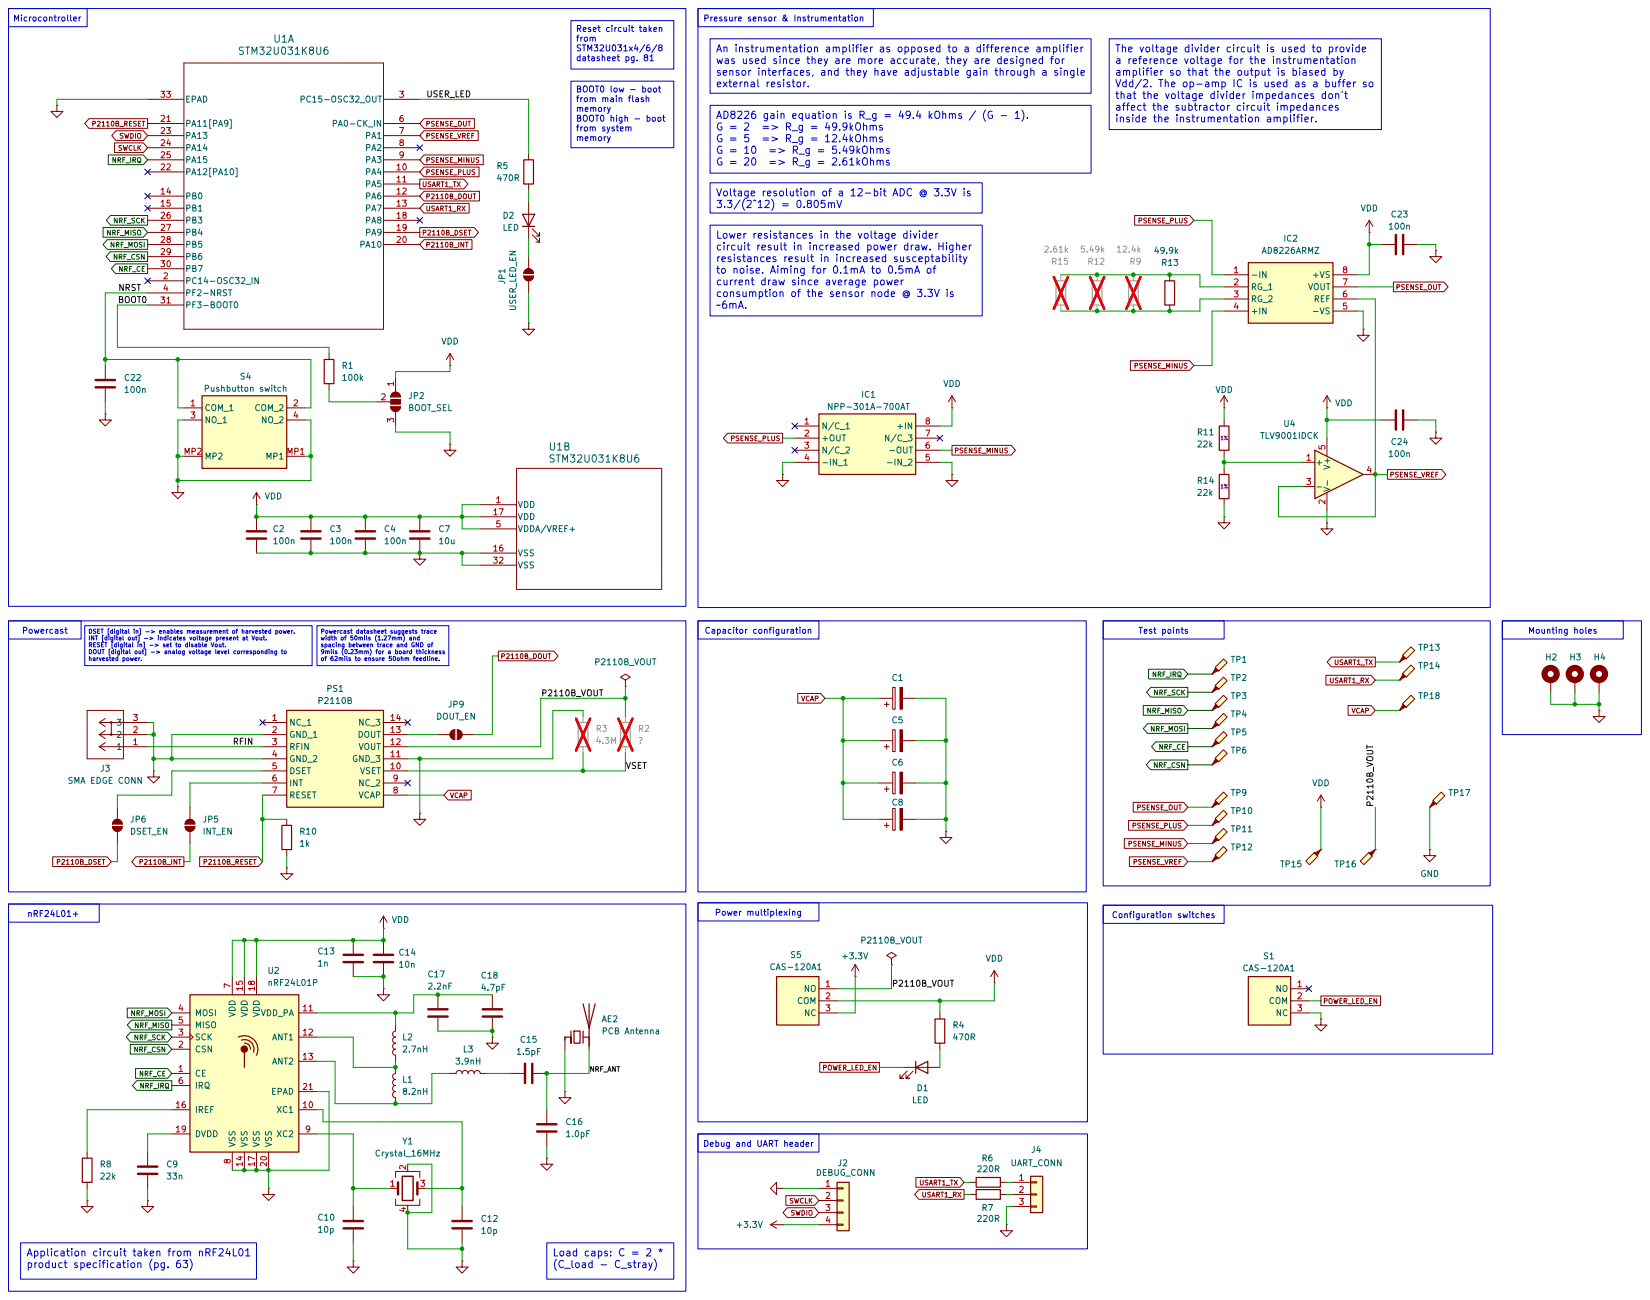
[picture p57: page 1]
