ardavan-p/elec-491/ptn/fw/Core/Src/ptn_control.c

/**
 * @file ptn_control.c
 * @author Ardavan Pourkeramati (ardavanpourkeramati@gmail.com)
 * @brief PTN control source file
 * @version 0.1
 * @date 2024-07-29
 * 
 * @copyright Copyright (c) 2024
 * 
 */

/* Headers */
#include "ptn_control.h"

void ptn_state_machine_run(void)
{
    // Initialize state machine

    // While loop
        // Process input
        // 
}
