ardavan-p/elec-491/ecu/Core/Src/can.c

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
/* Includes ------------------------------------------------------------------*/
#include "can.h"
#include "stm32f103xe.h"

CAN_HandleTypeDef hcan;

/* CAN init function */
void MX_CAN_Init(void) {

  hcan.Instance = CAN1;
  hcan.Init.Prescaler = 4;
  hcan.Init.Mode = CAN_MODE_NORMAL;
  hcan.Init.SyncJumpWidth = CAN_SJW_1TQ;
  hcan.Init.TimeSeg1 = CAN_BS1_13TQ;
  hcan.Init.TimeSeg2 = CAN_BS2_2TQ;
  hcan.Init.TimeTriggeredMode = DISABLE;
  hcan.Init.AutoBusOff = DISABLE;
  hcan.Init.AutoWakeUp = DISABLE;
  hcan.Init.AutoRetransmission = DISABLE;
  hcan.Init.ReceiveFifoLocked = DISABLE;
  hcan.Init.TransmitFifoPriority = DISABLE;
  if (HAL_CAN_Init(&hcan) != HAL_OK) {
    Error_Handler();
  }
}

void HAL_CAN_MspInit(CAN_HandleTypeDef *canHandle) {

  GPIO_InitTypeDef GPIO_InitStruct = {0};
  if (canHandle->Instance == CAN1) {
    /* CAN1 clock enable */
    __HAL_RCC_CAN1_CLK_ENABLE();

    __HAL_RCC_GPIOB_CLK_ENABLE();
    /**CAN GPIO Configuration
    PB8     ------> CAN_RX
    PB9     ------> CAN_TX
    */
    GPIO_InitStruct.Pin = GPIO_PIN_8;
    GPIO_InitStruct.Mode = GPIO_MODE_INPUT;
    GPIO_InitStruct.Pull = GPIO_NOPULL;
    HAL_GPIO_Init(GPIOB, &GPIO_InitStruct);

    GPIO_InitStruct.Pin = GPIO_PIN_9;
    GPIO_InitStruct.Mode = GPIO_MODE_AF_PP;
    GPIO_InitStruct.Speed = GPIO_SPEED_FREQ_HIGH;
    HAL_GPIO_Init(GPIOB, &GPIO_InitStruct);

    __HAL_AFIO_REMAP_CAN1_2();

    /* CAN1 interrupt Init */
    HAL_NVIC_SetPriority(USB_LP_CAN1_RX0_IRQn, 0, 0);
    HAL_NVIC_EnableIRQ(USB_LP_CAN1_RX0_IRQn);
  }
}

void HAL_CAN_MspDeInit(CAN_HandleTypeDef *canHandle) {

  if (canHandle->Instance == CAN1) {
    /* Peripheral clock disable */
    __HAL_RCC_CAN1_CLK_DISABLE();

    /**CAN GPIO Configuration
    PB8     ------> CAN_RX
    PB9     ------> CAN_TX
    */
    HAL_GPIO_DeInit(GPIOB, GPIO_PIN_8 | GPIO_PIN_9);

    /* CAN1 interrupt Deinit */
    HAL_NVIC_DisableIRQ(USB_LP_CAN1_RX0_IRQn);
  }
}

/* USER CODE BEGIN 1 */

HAL_StatusTypeDef HAL_CAN_AddTxMessagePolling(
    CAN_HandleTypeDef *hcan, const CAN_TxHeaderTypeDef *pHeader,
    const uint8_t aData[], uint32_t *pTxMailbox, uint32_t timeout) {
  HAL_StatusTypeDef status = HAL_OK;

  uint32_t start_time = HAL_GetTick();

  do {
    if (HAL_CAN_GetTxMailboxesFreeLevel(hcan) > 0) {
      status = HAL_CAN_AddTxMessage(hcan, pHeader, aData, pTxMailbox);
      return status;
    }
  } while (HAL_GetTick() - start_time <= timeout);

  return HAL_TIMEOUT;
}

HAL_StatusTypeDef HAL_CAN_GetRxMessagePolling(CAN_HandleTypeDef *hcan,
                                              uint32_t RxFifo,
                                              CAN_RxHeaderTypeDef *pHeader,
                                              uint8_t aData[],
                                              uint32_t timeout) {
  HAL_StatusTypeDef status = HAL_OK;

  uint32_t start_time = HAL_GetTick();

  do {
    if (HAL_CAN_GetRxFifoFillLevel(hcan, CAN_RX_FIFO0) > 0) {
      status = HAL_CAN_GetRxMessage(hcan, RxFifo, pHeader, aData);
      return status;
    }
  } while (HAL_GetTick() - start_time <= timeout);

  return HAL_TIMEOUT;
}

/* USER CODE END 1 */
