ardavan-p/elec-491/ecu/Core/Inc/can.h

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
/* Define to prevent recursive inclusion -------------------------------------*/
#ifndef __CAN_H__
#define __CAN_H__

#ifdef __cplusplus
extern "C" {
#endif

/* Includes ------------------------------------------------------------------*/
#include "main.h"

extern CAN_HandleTypeDef hcan;

/* USER CODE BEGIN Private defines */

#define CAN_MSG_FRAME_LEN_BYTES (8)
#define PTN_REQUEST_ID (0x101)
#define PTN_RESPONSE_ID (0x100)
#define PTN_RESET_ID (0x102)

/* USER CODE END Private defines */

void MX_CAN_Init(void);

/* USER CODE BEGIN Prototypes */

HAL_StatusTypeDef HAL_CAN_AddTxMessagePolling(
    CAN_HandleTypeDef *hcan, const CAN_TxHeaderTypeDef *pHeader,
    const uint8_t aData[], uint32_t *pTxMailbox, uint32_t timeout);

HAL_StatusTypeDef HAL_CAN_GetRxMessagePolling(CAN_HandleTypeDef *hcan,
                                              uint32_t RxFifo,
                                              CAN_RxHeaderTypeDef *pHeader,
                                              uint8_t aData[],
                                              uint32_t timeout);

/* USER CODE END Prototypes */

#ifdef __cplusplus
}
#endif

#endif /* __CAN_H__ */
